danyaliqbal88/bthealthapp/Riko Chi/ADC/ADC board.PNG

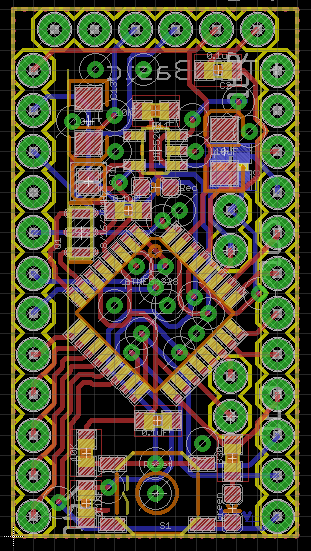
Riko Chi/ADC/ADC board.PNG
