danyaliqbal88/bthealthapp/Riko Chi/c12666schematic.png

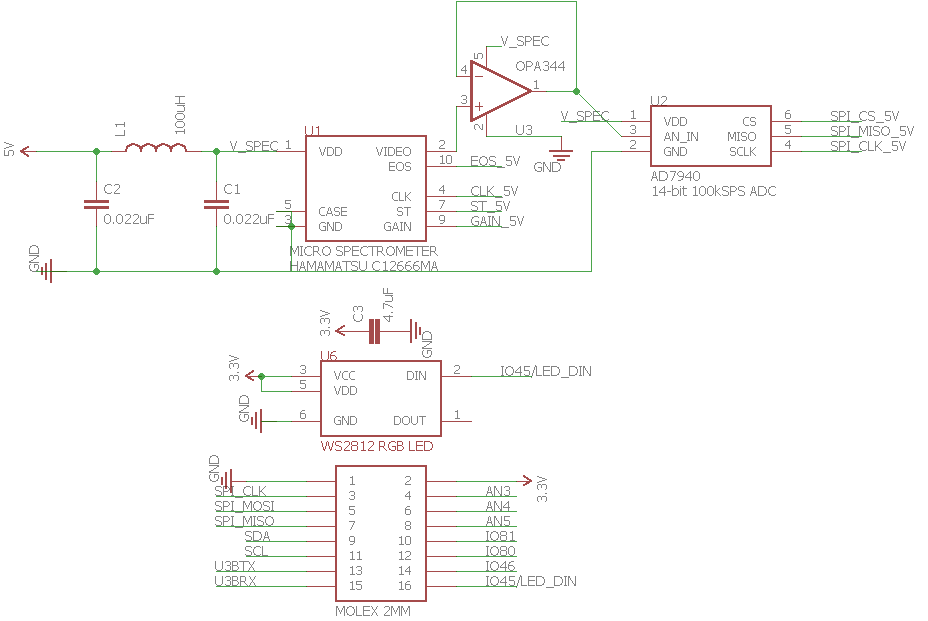
Riko Chi/c12666schematic.png
