danyaliqbal88/bthealthapp/Riko Chi/ECG AFE eagle files/ECG AFE board.PNG

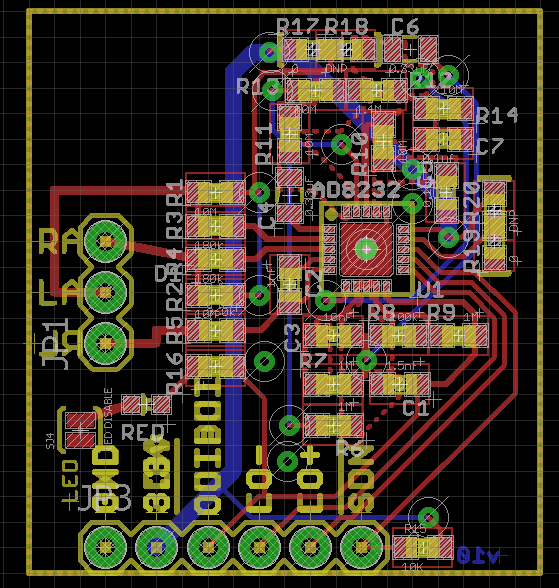
Riko Chi/ECG AFE eagle files/ECG AFE board.PNG
