danyaliqbal88/bthealthapp/Riko Chi/ECG AFE eagle files/ECG AFE schematic.PNG

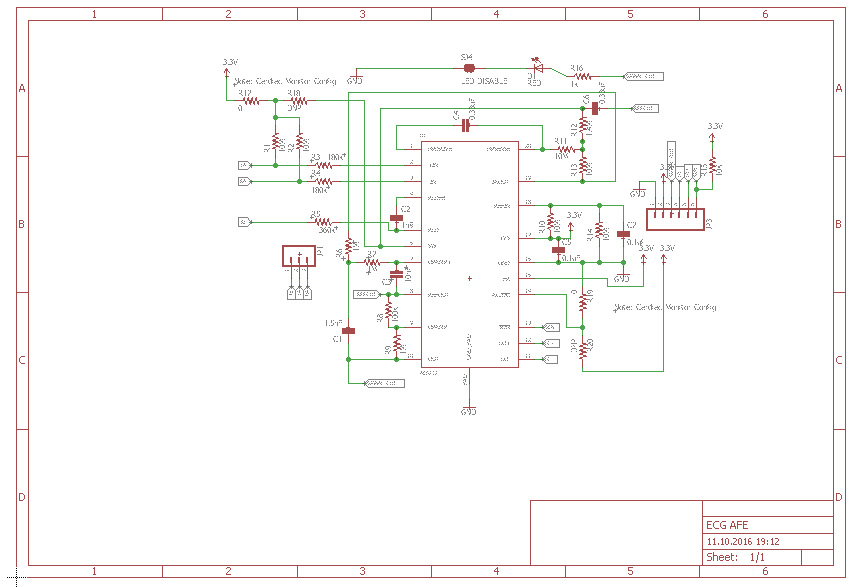
Riko Chi/ECG AFE eagle files/ECG AFE schematic.PNG
