danyaliqbal88/bthealthapp/Riko Chi/PPG AFE design files/mini PPG schematic.PNG

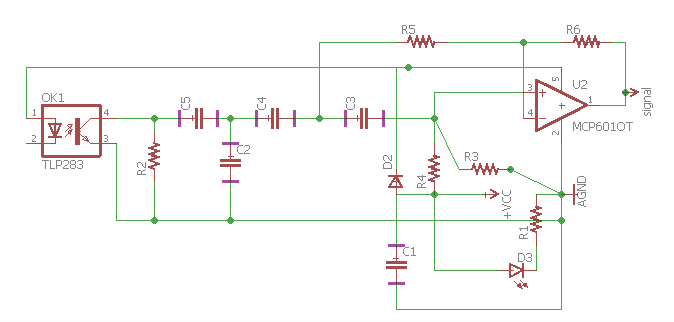
Riko Chi/PPG AFE design files/mini PPG schematic.PNG
