danyaliqbal88/bthealthapp/Riko Chi/3d printable watch housing/1.PNG

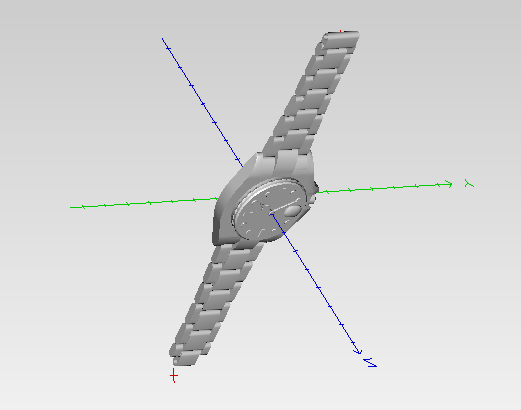
Riko Chi/3d printable watch housing/1.PNG
