danyaliqbal88/bthealthapp/Riko Chi/3d printable watch housing/3.PNG

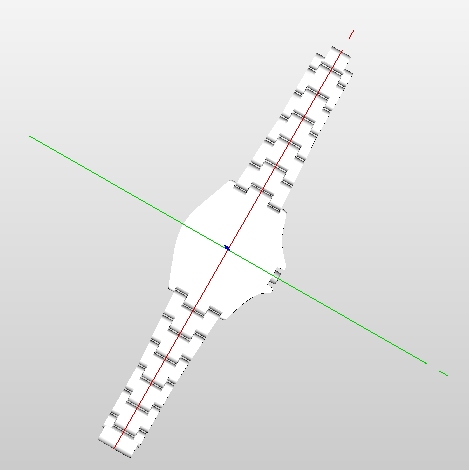
Riko Chi/3d printable watch housing/3.PNG
