danyaliqbal88/bthealthapp/Riko Chi/3d printable watch housing/4.PNG

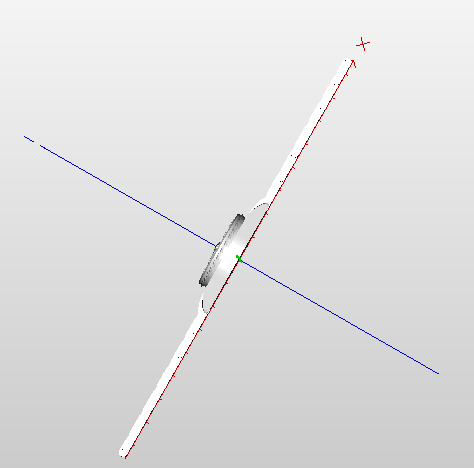
Riko Chi/3d printable watch housing/4.PNG
