danyaliqbal88/bthealthapp/Riko Chi/3d printable watch housing/bezl_winder.PNG

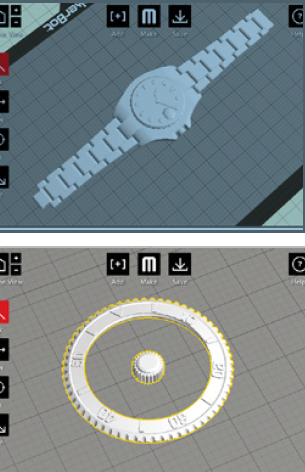
Riko Chi/3d printable watch housing/bezl_winder.PNG
