danyaliqbal88/bthealthapp/Riko Chi/3d printable watch housing/bezl_winder_2.PNG

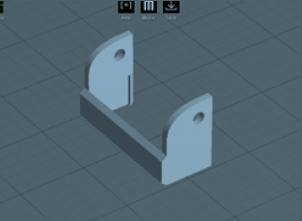
Riko Chi/3d printable watch housing/bezl_winder_2.PNG
