danyaliqbal88/bthealthapp/Riko Chi/3d printable watch housing/raseed iphone.PNG

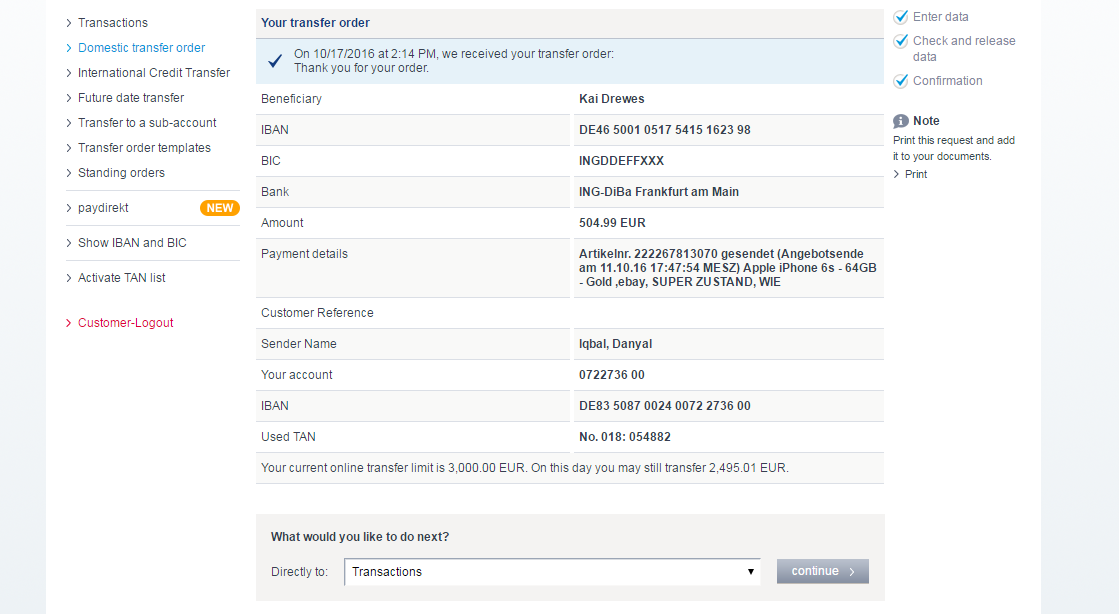
Riko Chi/3d printable watch housing/raseed iphone.PNG
