danyaliqbal88/bthealthapp/Riko Chi/3d printable watch housing/raseed soid.PNG

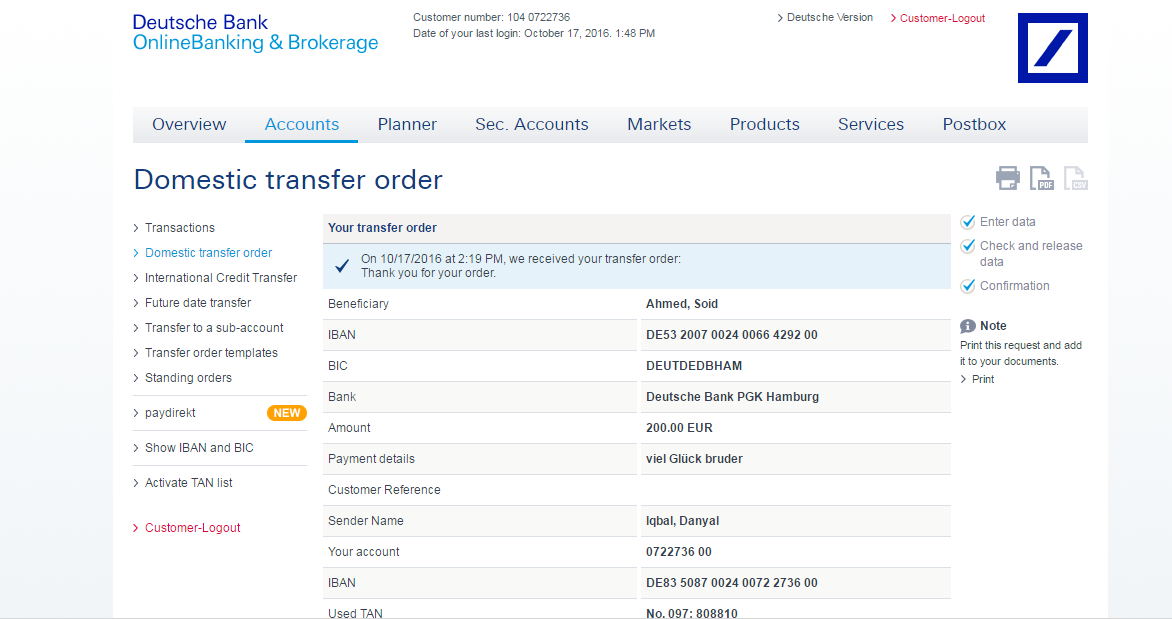
Riko Chi/3d printable watch housing/raseed soid.PNG
